institut-galilee/Immersion_projects/Test Arduino/TCS3200/IMAGE TEST2.png

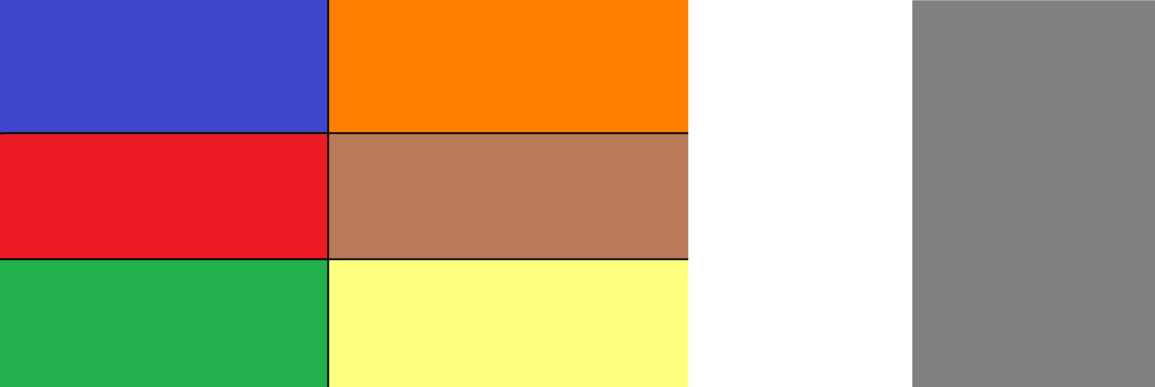
Test Arduino/TCS3200/IMAGE TEST2.png
